monotech/NuXT/Images/Profile.png

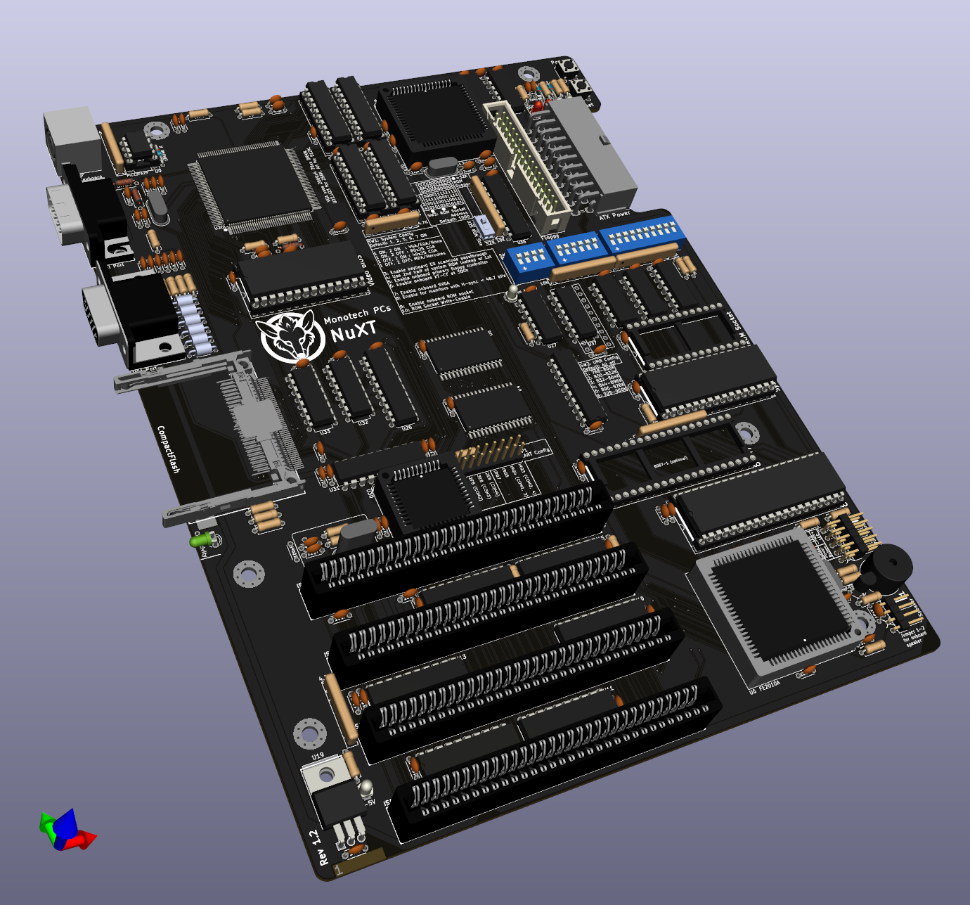
Images/Profile.png
