monotech/NuXT/Micro 8088 Memory Map.png

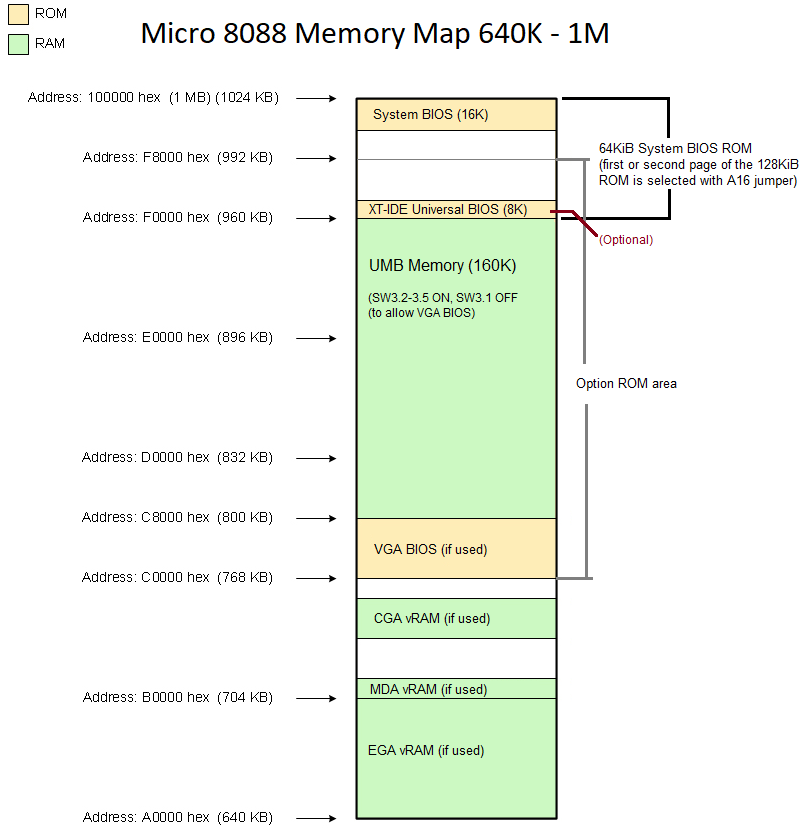
Micro 8088 Memory Map.png
