monotech/NuXT/MicroATX Pattern.png

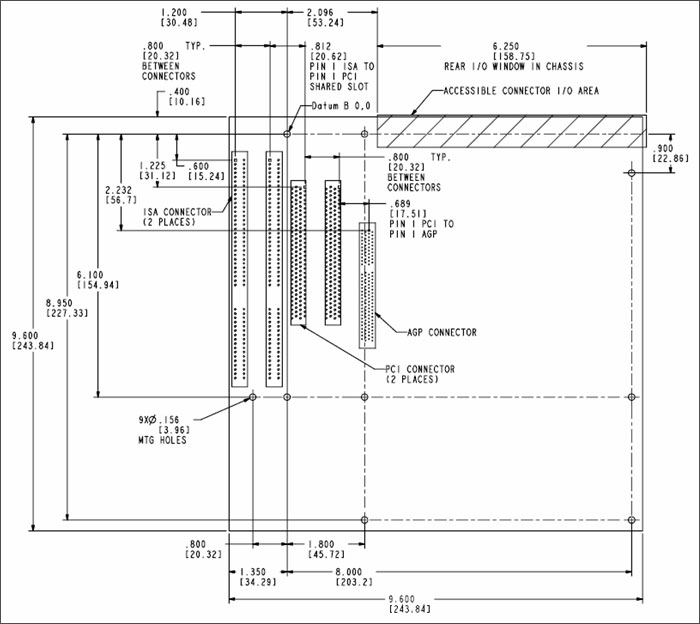
MicroATX Pattern.png
